basilfx/RNGstick/docs/adc_3bits.png

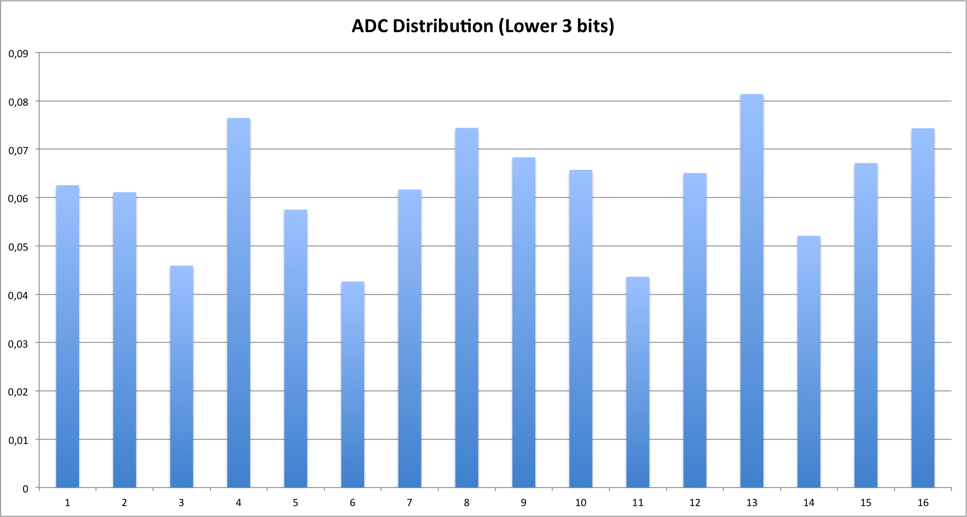
docs/adc_3bits.png
