basilfx/RNGstick/contrib/collector.py

import itertools
import serial
import time
import sys

# Number of bytes per test to collect
COUNT = 1024 * 128  # 256kb

# Properties to vary
PROPERTIES = {
    "sampleReset": [0, 1],
    "sampleBucket": [1, 256],
    "sampleMultiple": [1, 128],
    "delayHold": [0, 100],
    "delaySkip": [0, 100],
    "delayRound": [0],
    "sampleMask": [0b00011111, 0b00001111],
    "sampleShift": [0],
    "sampleTake": [5, 4],
    "mode": [1, 2],
    "extractor": [1, 2, 3],
    "generator": [1],
    "output": [1, 2],
    "outputMode": [1],
    "outputBucket": [1]
}


def main():
    # Determine all possible combinations
    names = sorted(PROPERTIES)
    combinations = [
        {k: v for k, v in zip(names, product)}
        for product in itertools.product(*(PROPERTIES[name] for name in names))
    ]

    # Open serial device
    device = serial.Serial(sys.argv[1], baudrate=115200, dsrdtr=True)

    # Start iterating
    sys.stdout.write("In total, %d to execute\n" % len(combinations))

    for index, combination in enumerate(combinations):
        data = bytearray()

        # Info
        sys.stdout.write(
            "Executing test %d/%d\n" % (index + 1, len(combinations)))

        # Skip some tests
        if index < 880:
            continue

        # Reset Arduino
        device.setDTR(False)
        time.sleep(0.5)
        device.setDTR(True)
        time.sleep(4.0)

        device.write("\r\n")
        time.sleep(1.0)

        # Set the settings
        for key, value in combination.iteritems():
            device.write("%s %s\r\n" % (key, value))
            time.sleep(0.5)

        # Start data collection
        device.write("run\r\n")
        device.flushInput()

        while len(data) < COUNT:
            data.extend(device.read(1024))

            sys.stdout.write("\r%d/%d bytes" % (len(data), COUNT))
            sys.stdout.flush()

        # Write output
        with open("test_%d.bin" % index, "wb") as fp:
            fp.write(data)

        with open("test_%d.txt" % index, "w") as fp:
            fp.write(str(combination))


# E.g. `python runner.py /dev/ttyACM0`
if __name__ == "__main__":
    sys.exit(main())
